daprice/ios-macropad/Acrylic case/layout.scad

u = [19.05, 19.05];

key_layout = [
	[1,    [[1,1], [1,1], [1,1]]],
	[0.25, []                   ],
	[1,    [[1,1], [1,1], [1,1]]],
	[1,    [[1,1], [1,1], [1,1]]],
	[1,    [[1,1], [1,1], [1,1]]],
];

col_offsets = [
	        0,    0,    0
];
